flummer/dmm-sao/IMAGES/DSC_0819.jpg

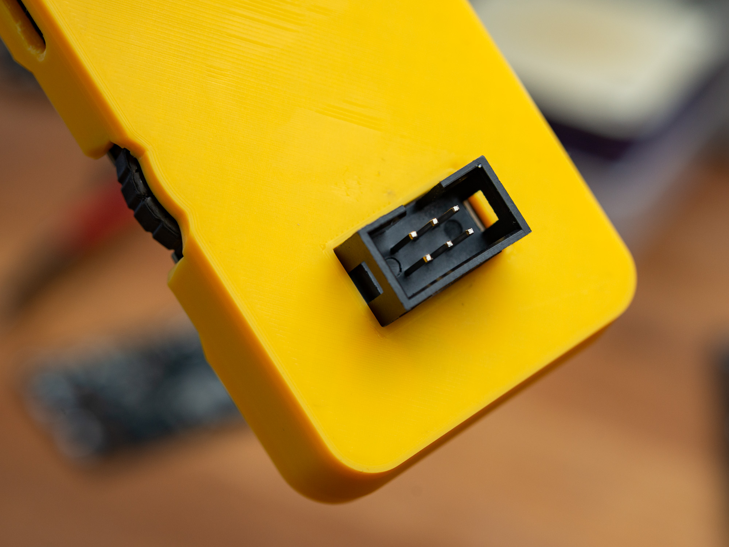
IMAGES/DSC_0819.jpg
