flummer/dmm-sao/IMAGES/DSC_0822.jpg

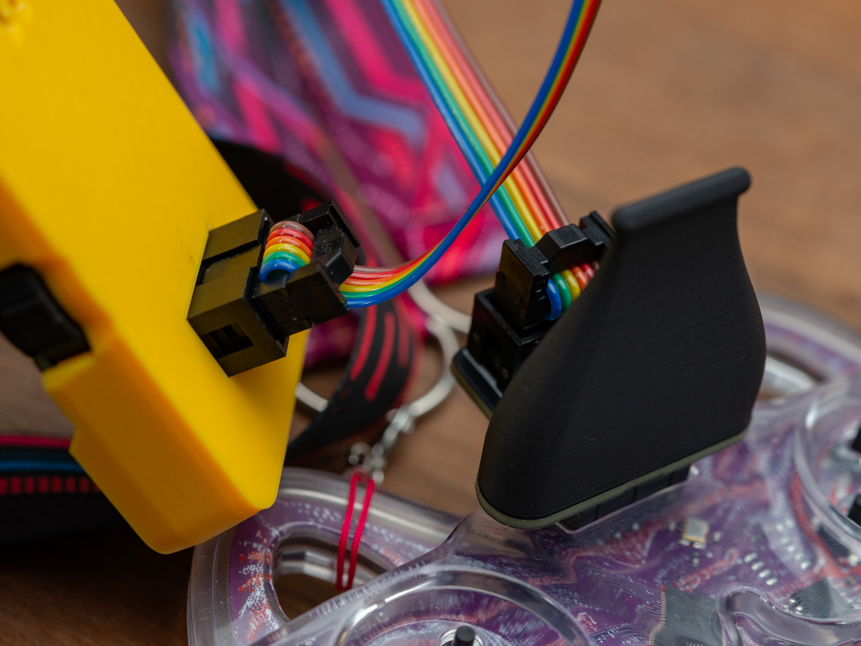
IMAGES/DSC_0822.jpg
